AugustoS97/CanBus-Radio-VAG/Images/PCB-render-bottom.png

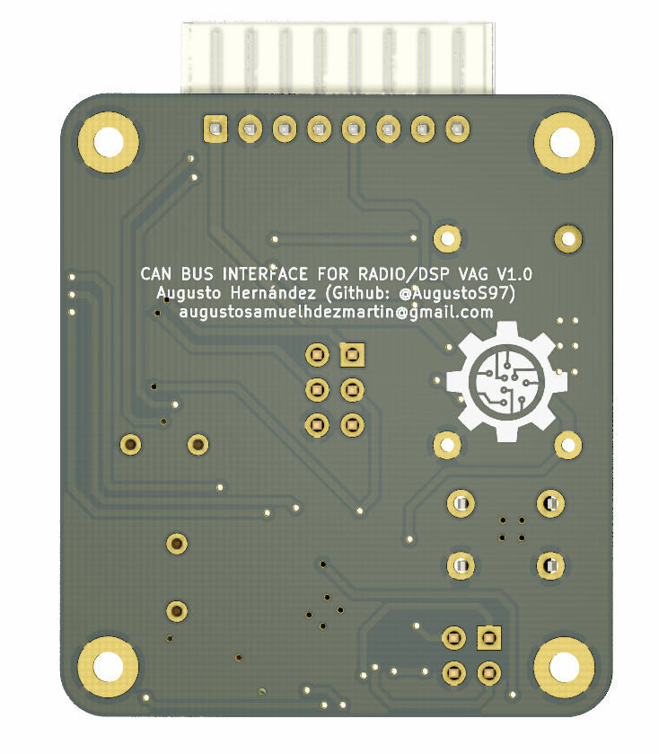
Images/PCB-render-bottom.png
