AugustoS97/CanBus-Radio-VAG/Arduino/tools/Can-Radio-tester/Can-Radio-tester.ino

/* Tool to read the CAN BUS and check if the Radio Interface is working well.
 * Return by serial all the can messages received.
 * Author: Augusto Samuel Hernandez Martin (Github: @AugustoS97)
 */

#include <SPI.h>
#include <mcp2515.h>

struct can_frame canMsg;
MCP2515 mcp2515(10);


void setup() {
  Serial.begin(115200);
  
  mcp2515.reset();
  mcp2515.setBitrate(CAN_100KBPS, MCP_8MHZ);
  mcp2515.setNormalMode();
  
  Serial.println("------- CAN Read ----------");
  Serial.println("ID  DLC   DATA");
}

void loop() {
  if (mcp2515.readMessage(&canMsg) == MCP2515::ERROR_OK) {
    Serial.print(canMsg.can_id, HEX); // print ID
    Serial.print(" "); 
    Serial.print(canMsg.can_dlc, HEX); // print DLC
    Serial.print(" ");
    
    for (int i = 0; i<canMsg.can_dlc; i++)  {  // print the data
      Serial.print(canMsg.data[i],HEX);
      Serial.print(" ");
    }

    Serial.println();      
  }
}
